D0ana/InfoEducatie_Barcainatorul/CAD/R&D/Beta0/Structura/Fuselaj/Fuselajv2_2.stl

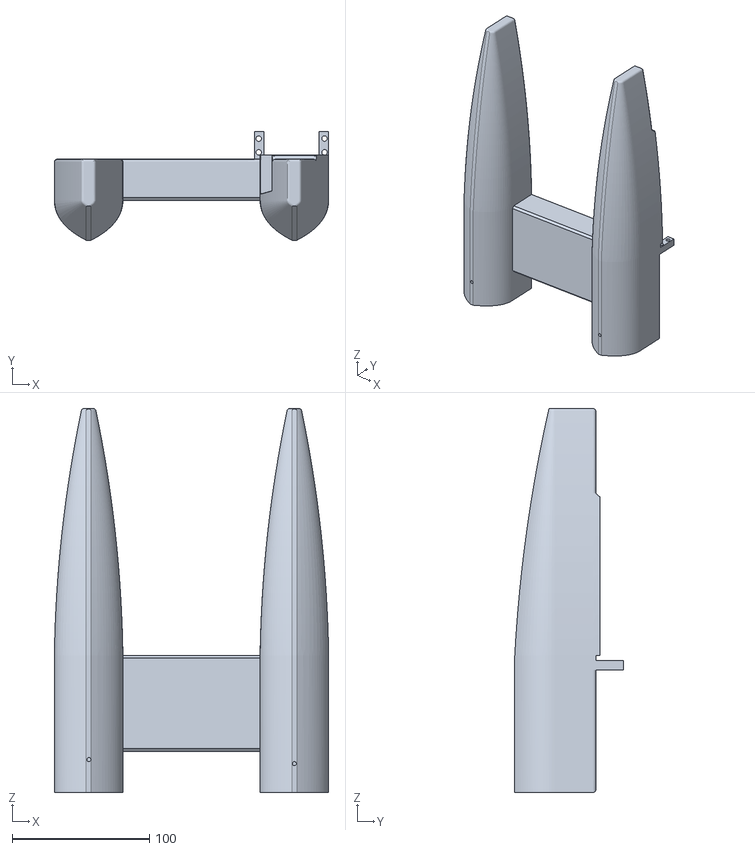
[picture p42: CAD file, 2021-04-29]
CAD/R&D/Beta0/Structura/Fuselaj/Fuselajv2_2.stl
200.0 x 79.1 x 280.0
